CopperMaiden/bluejaw/Images/20251108_200927.jpg

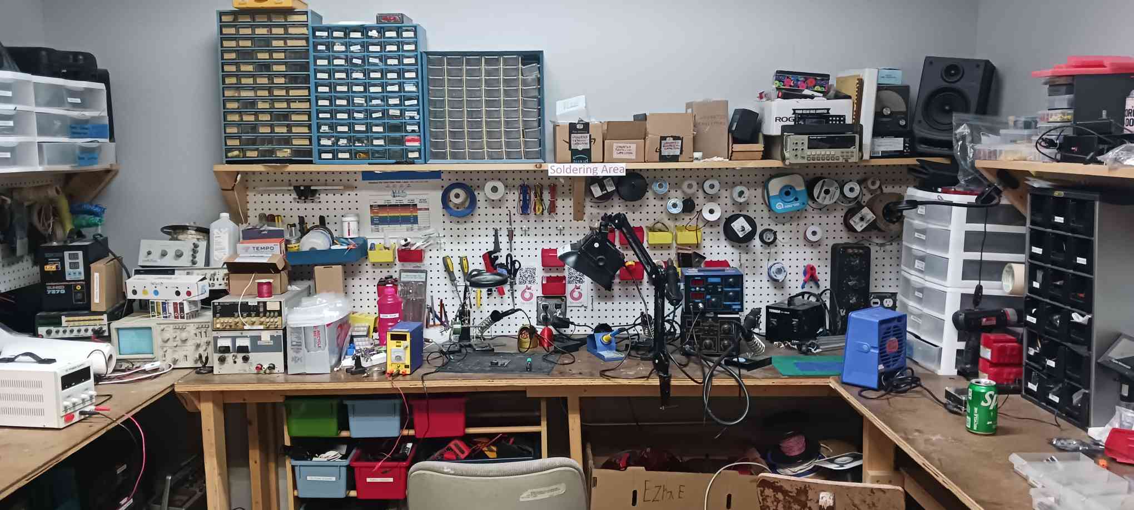
Images/20251108_200927.jpg
