CopperMaiden/bluejaw/Images/20260107_203826.jpg

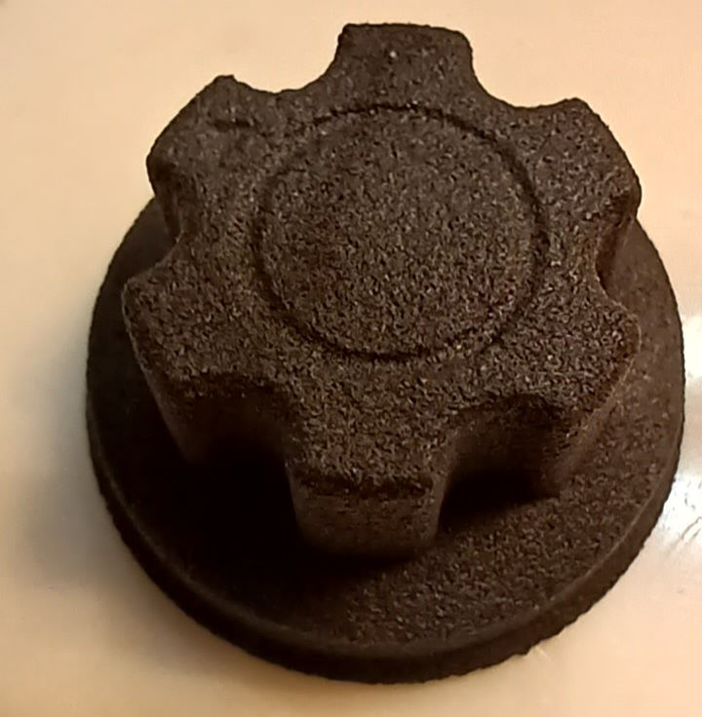
Images/20260107_203826.jpg
