CopperMaiden/bluejaw/Images/20260107_230642.jpg

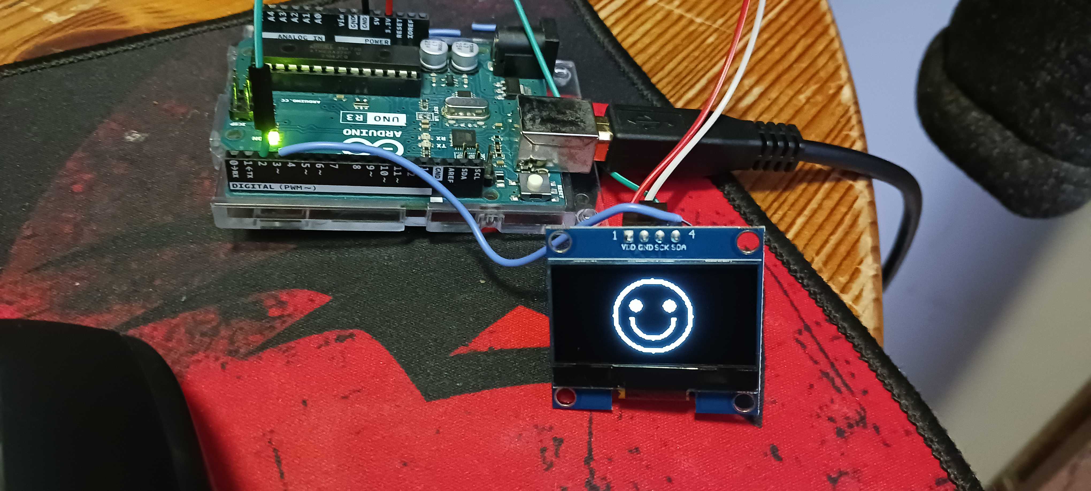
Images/20260107_230642.jpg
