CopperMaiden/bluejaw/Images/BLUEJAW(1).jpg

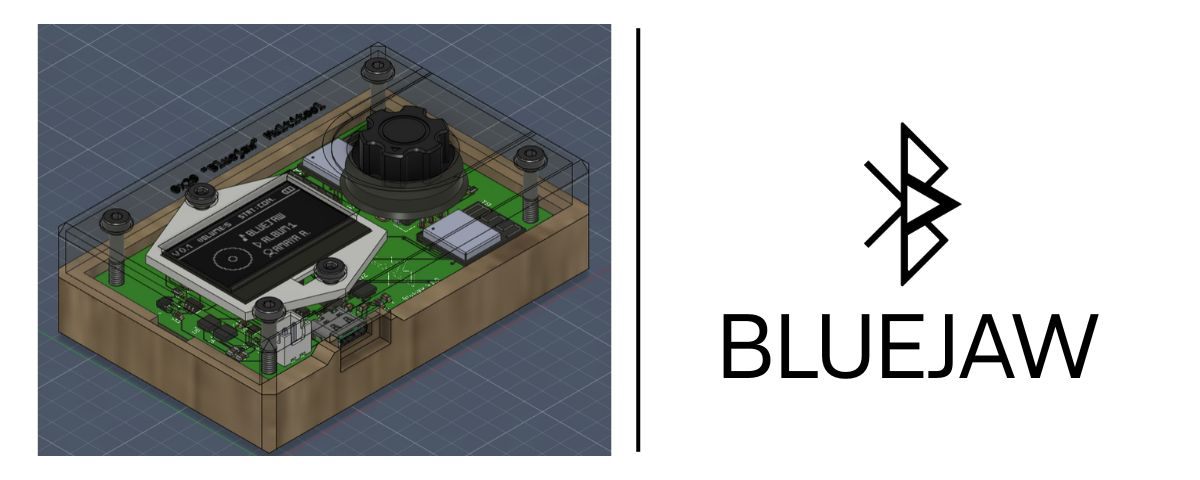
Images/BLUEJAW(1).jpg
