CopperMaiden/bluejaw/Images/BLUEJAW(2).jpg

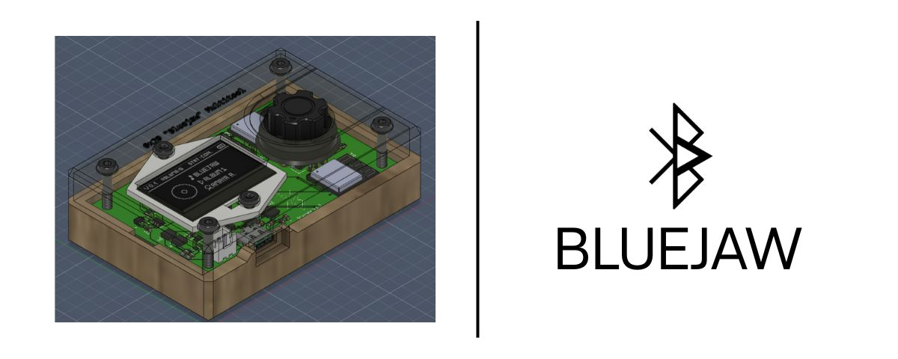
Images/BLUEJAW(2).jpg
