CopperMaiden/bluejaw/Images/BLUEJAW.jpg

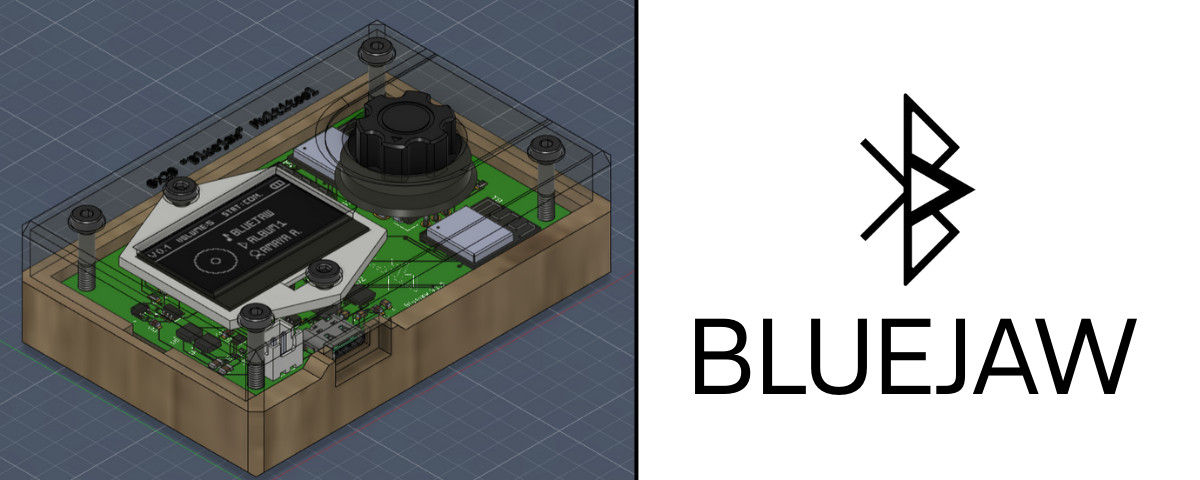
Images/BLUEJAW.jpg
