CopperMaiden/bluejaw/Images/image1.png

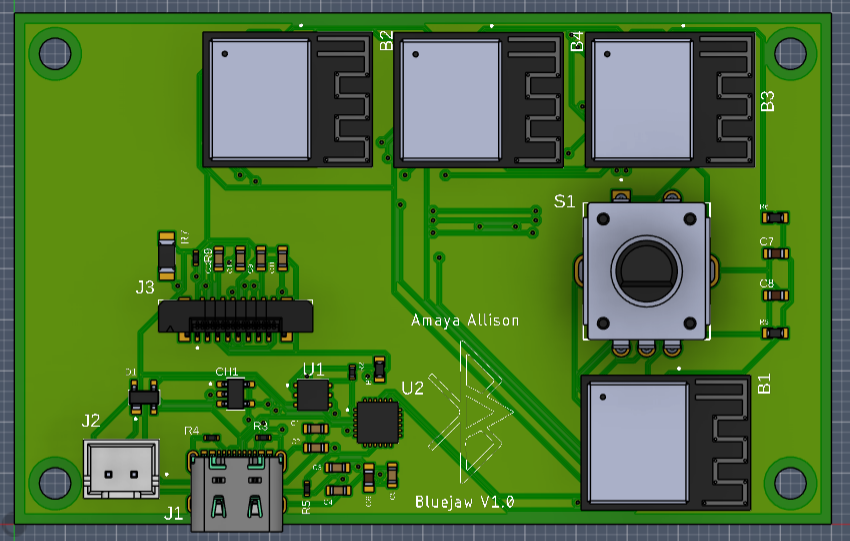
Images/image1.png
