CopperMaiden/bluejaw/Images/image2.png

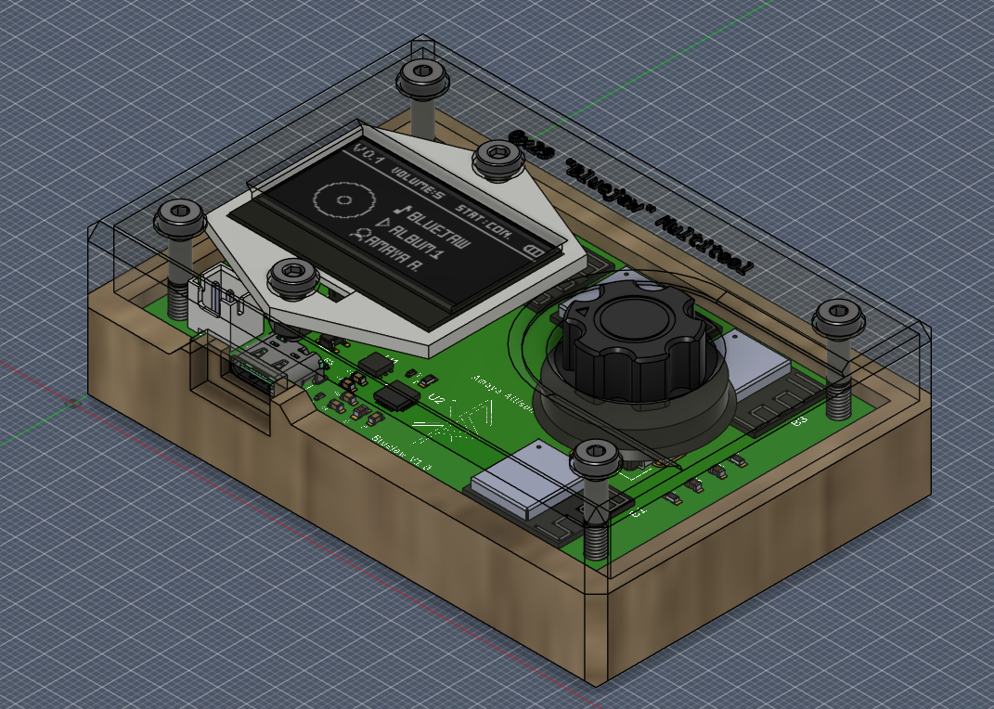
Images/image2.png
