CopperMaiden/bluejaw/Images/image3.png

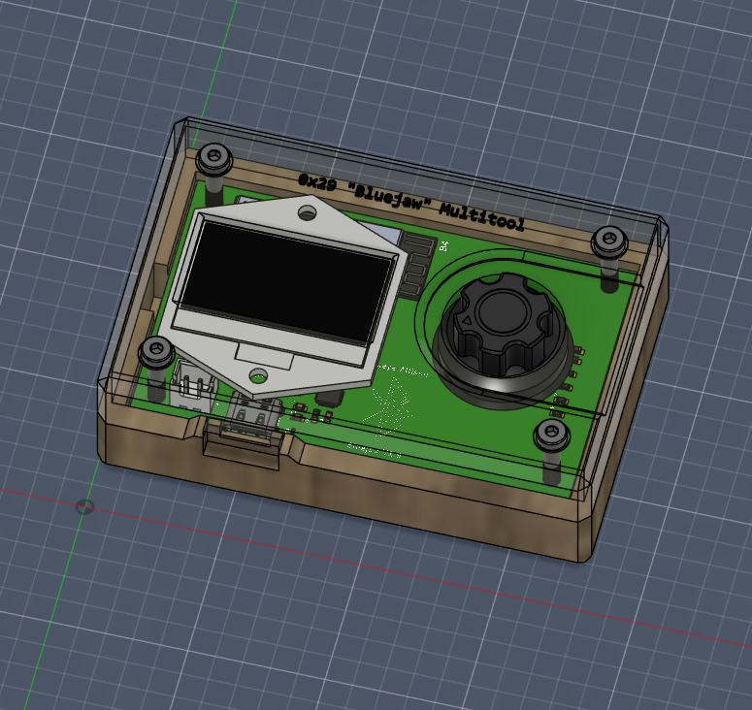
Images/image3.png
