CopperMaiden/bluejaw/Images/image4.png

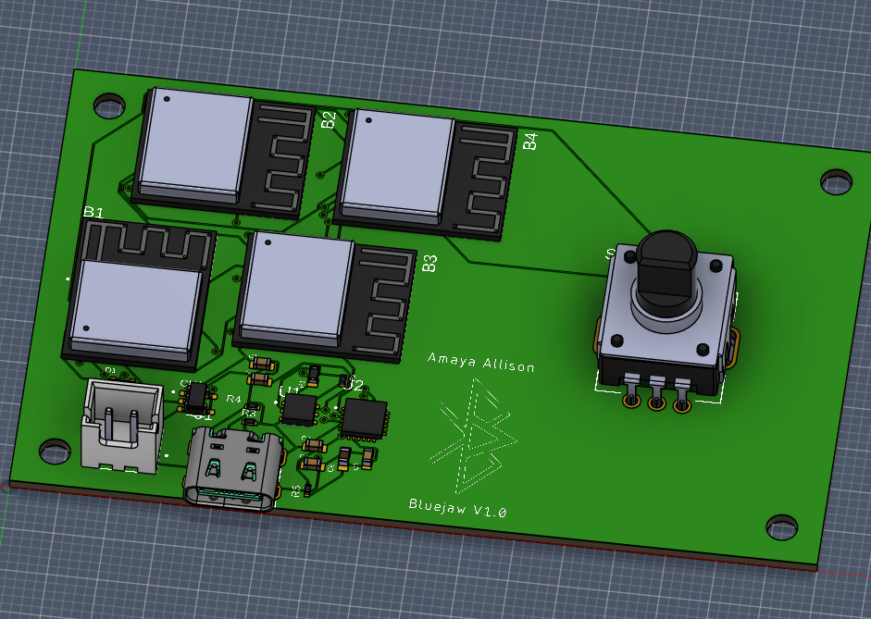
Images/image4.png
