CopperMaiden/bluejaw/Images/image5.png

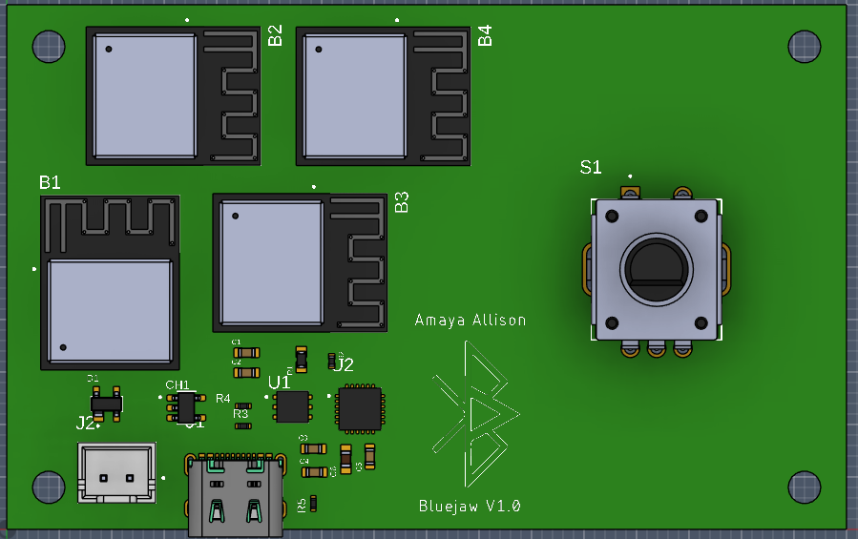
Images/image5.png
