CopperMaiden/bluejaw/Images/image6.png

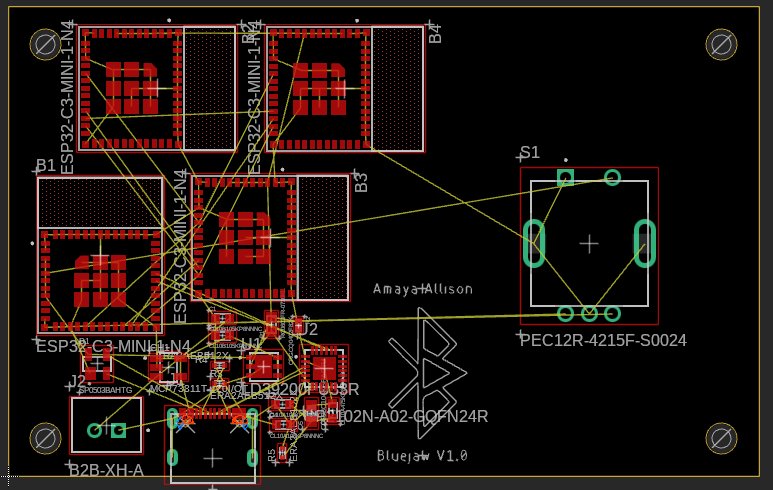
Images/image6.png
