CopperMaiden/bluejaw/Images/image7.png

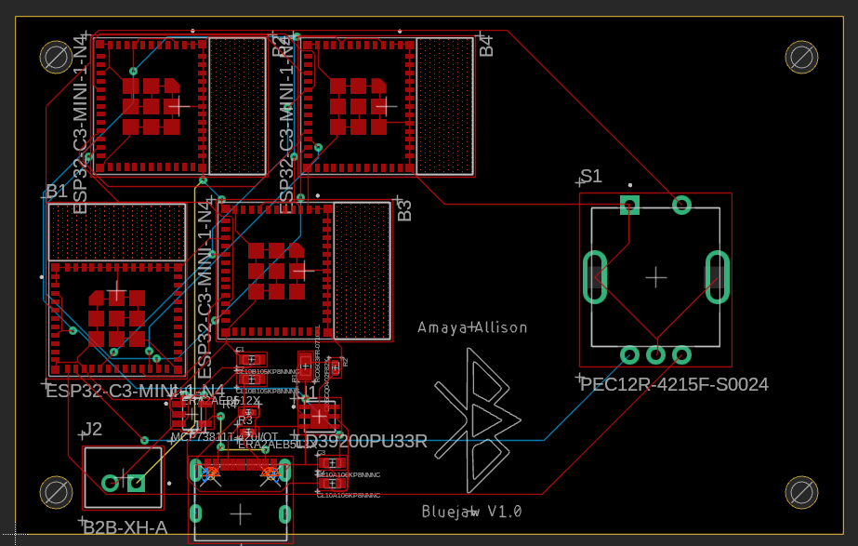
Images/image7.png
