CopperMaiden/bluejaw/Images/image8.png

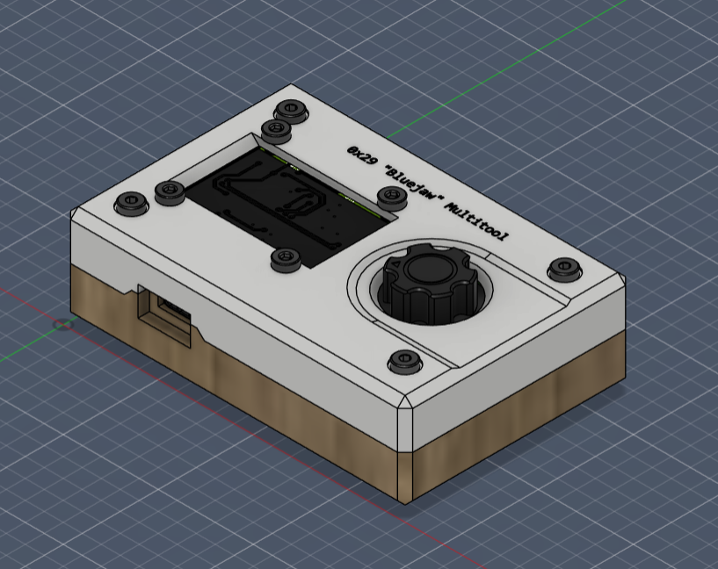
Images/image8.png
