CopperMaiden/bluejaw/Images/image10.png

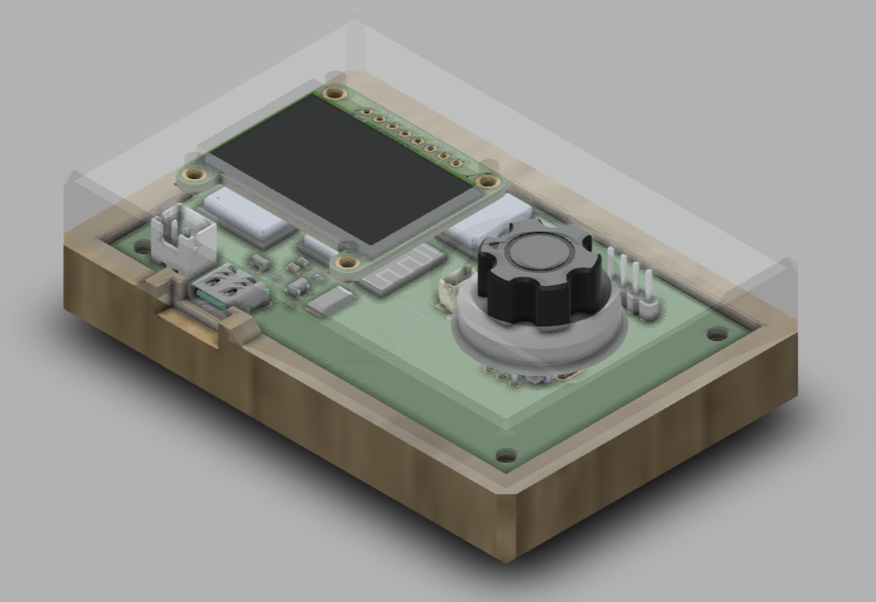
Images/image10.png
