CopperMaiden/bluejaw/Images/image11.png

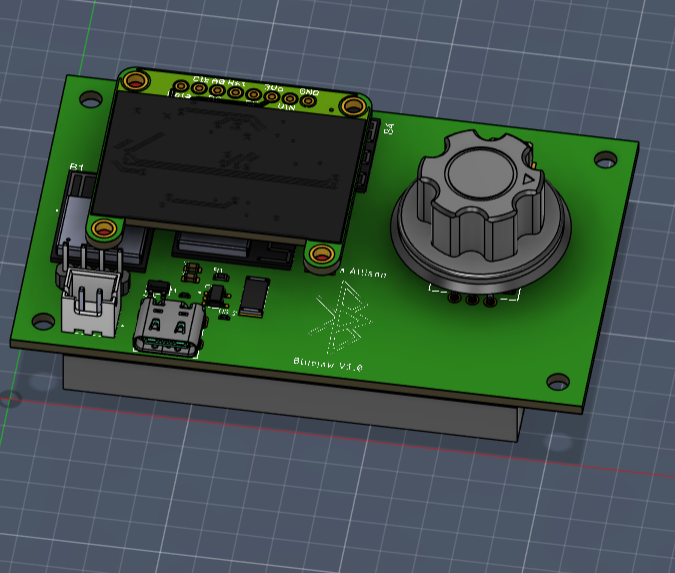
Images/image11.png
