CopperMaiden/bluejaw/Images/image12.png

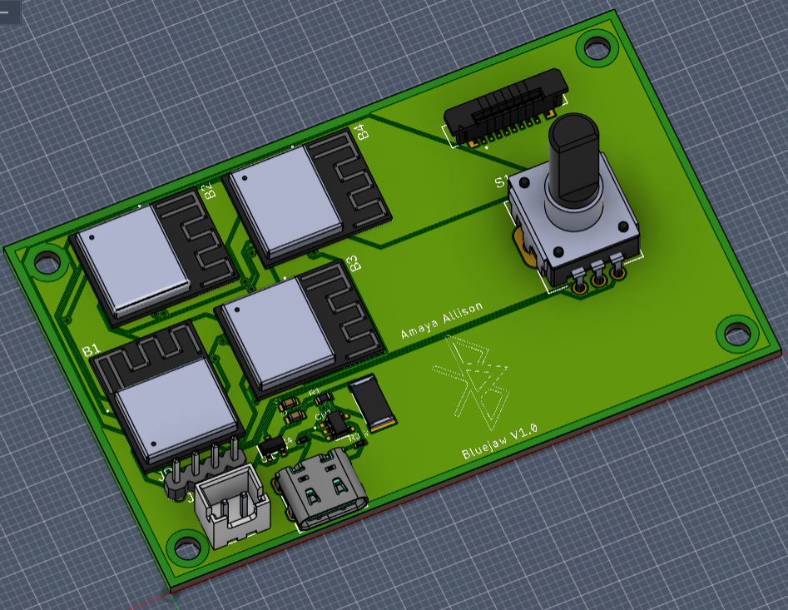
Images/image12.png
