CopperMaiden/bluejaw/Images/image13.png

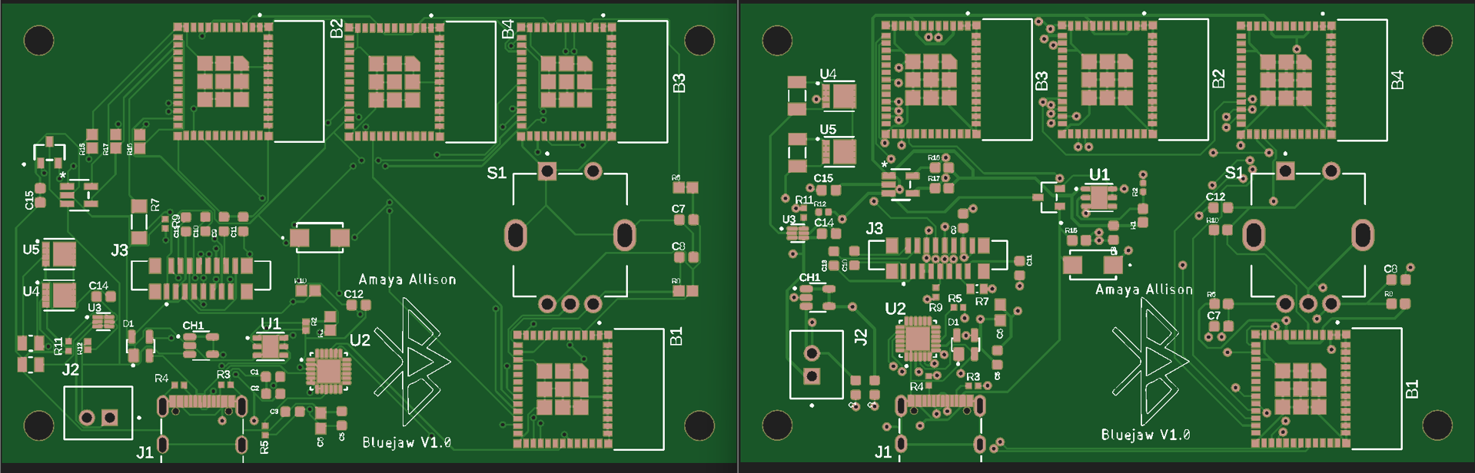
Images/image13.png
