CopperMaiden/bluejaw/Images/image14.png

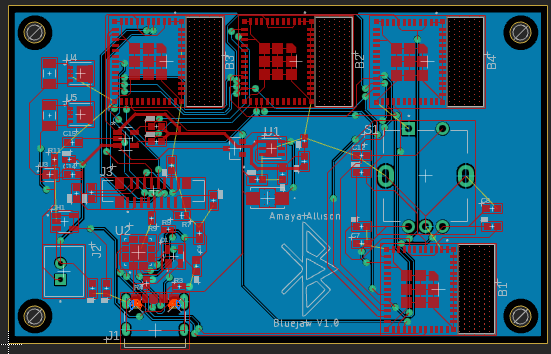
Images/image14.png
