CopperMaiden/bluejaw/Images/image15.png

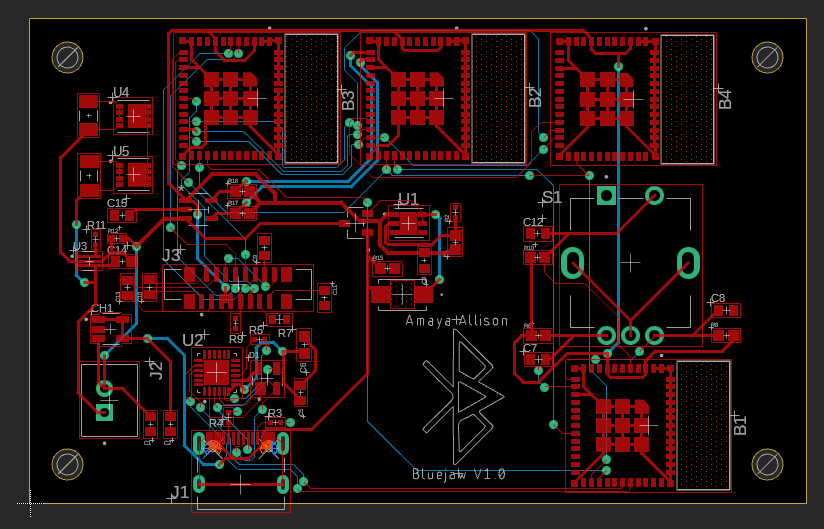
Images/image15.png
