CopperMaiden/bluejaw/Images/image16.png

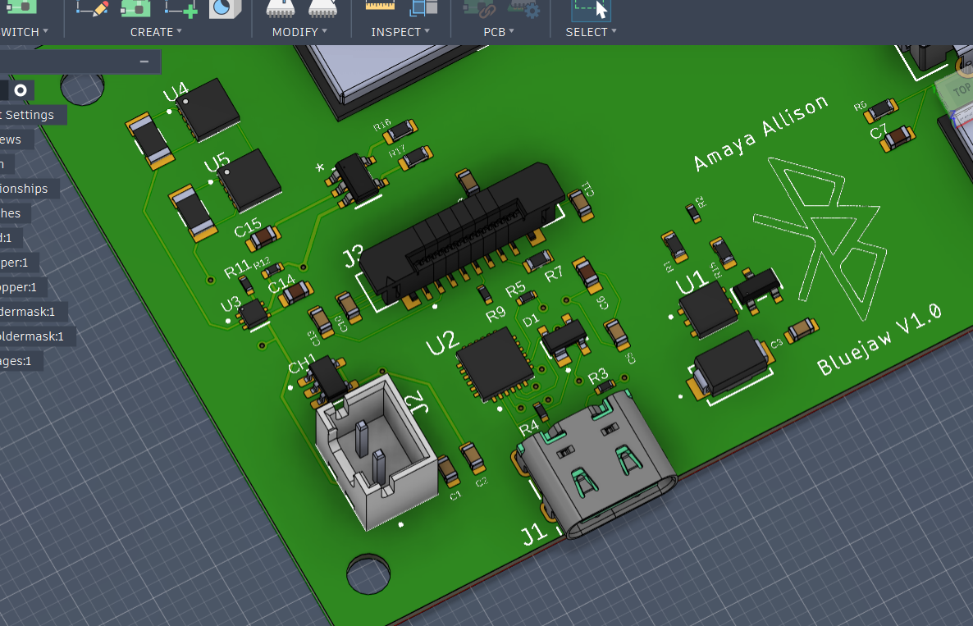
Images/image16.png
