CopperMaiden/bluejaw/Images/image-9.png

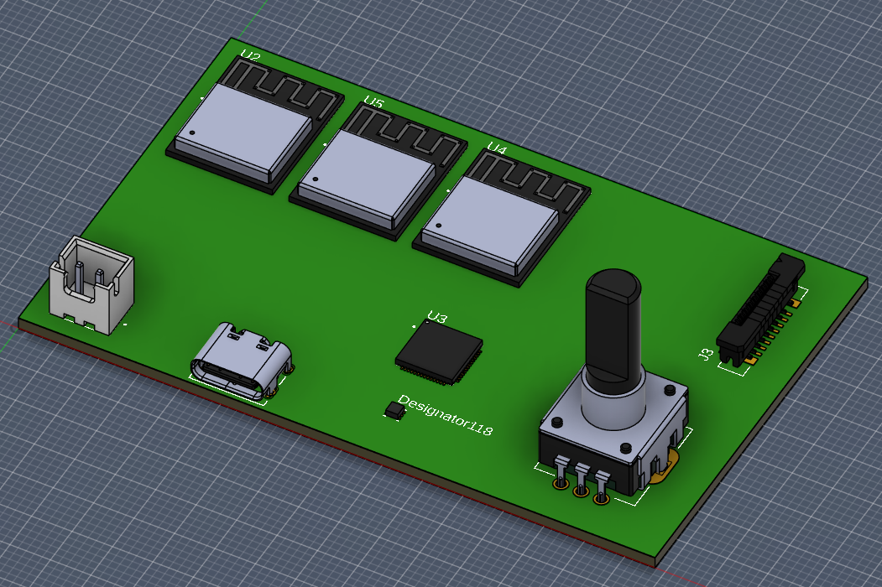
Images/image-9.png
