CopperMaiden/bluejaw/Images/image.png

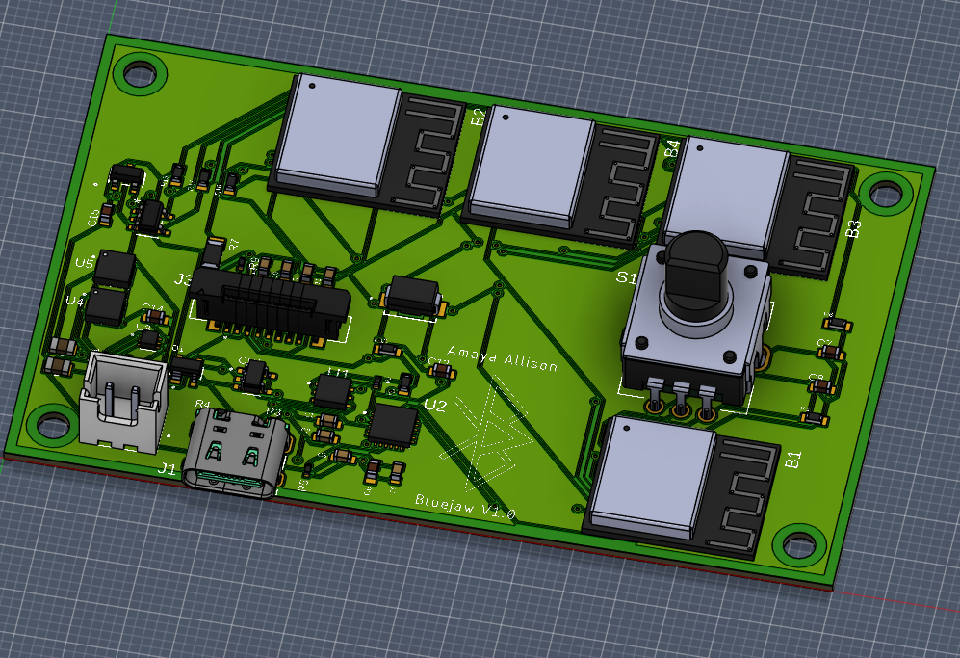
Images/image.png
