CopperMaiden/bluejaw/Images/Screenshot 2026-02-08 073245.png

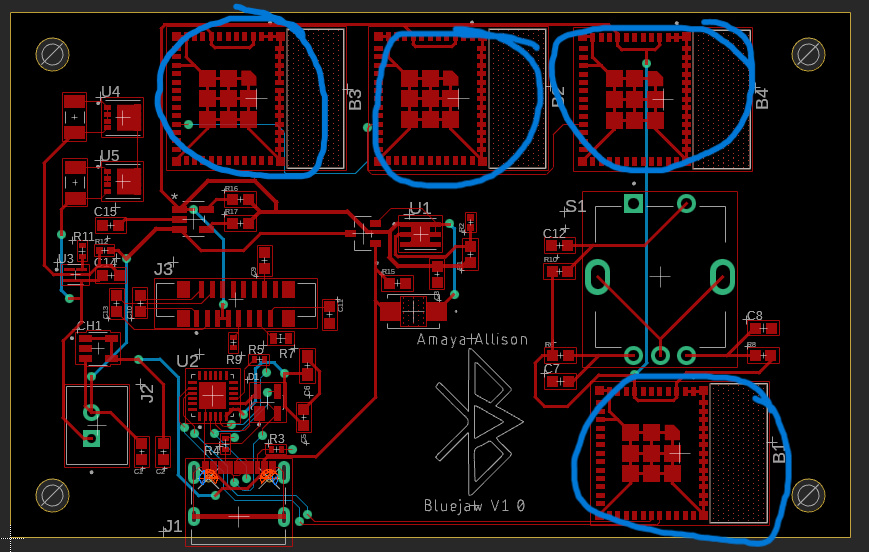
Images/Screenshot 2026-02-08 073245.png
