CopperMaiden/bluejaw/Images/Untitled design.png

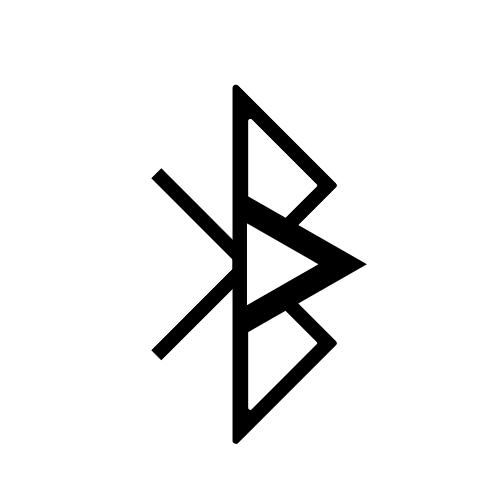
Images/Untitled design.png
